klouderone/cornev4promicroedition/Cases/OLED Covers/No Display Cover Right.stp

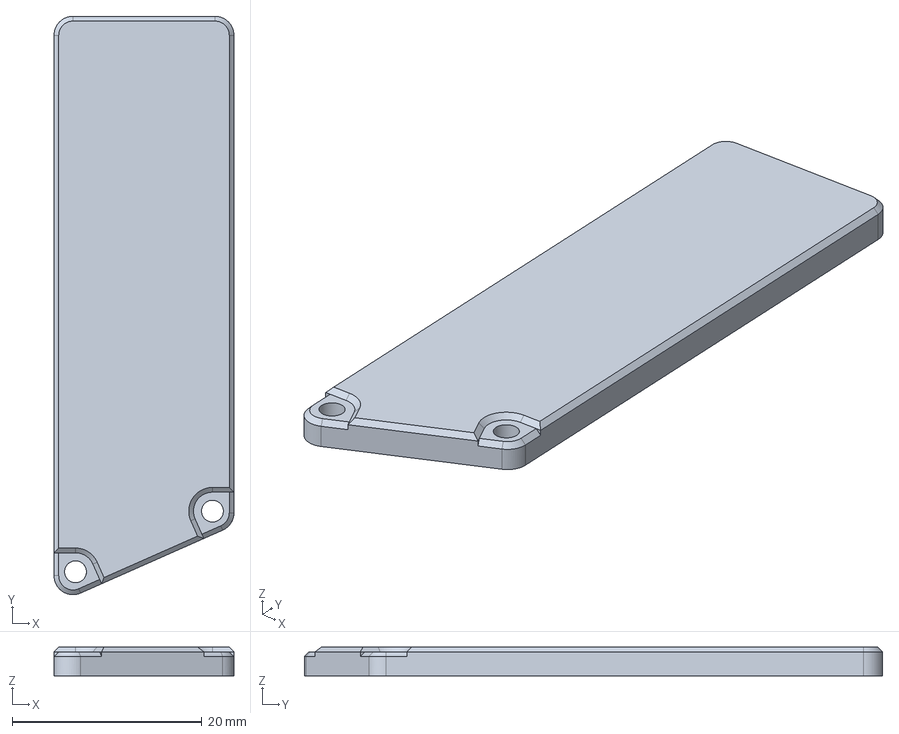
[picture p11: CAD file, 2025-02-16]
Cases/OLED Covers/No Display Cover Right.stp
19.0 x 61.0 x 3.05 mm
