klouderone/cornev4promicroedition/Cases/Switch Plates/Corne V4 PME MX 5 Column Switch Plate Right.stp

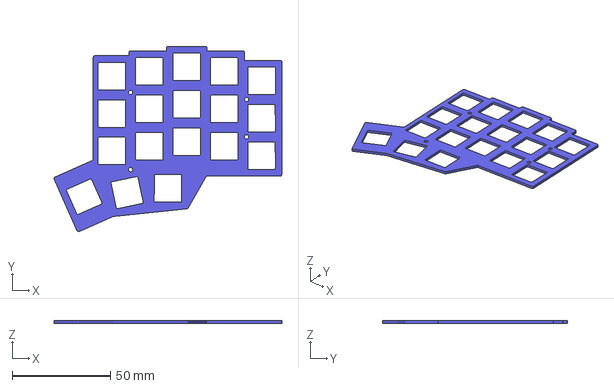
[picture p12: CAD file, 2025-02-16]
Cases/Switch Plates/Corne V4 PME MX 5 Column Switch Plate Right.stp
116.1 x 94.4 x 1.35 mm
