klouderone/cornev4promicroedition/Corne V4 Pro Micro Edition Kicad/left.kicad_sch

## KiCad design Corne V4 Pro Micro Edition Kicad/left.kicad_sch (2025-02-16)

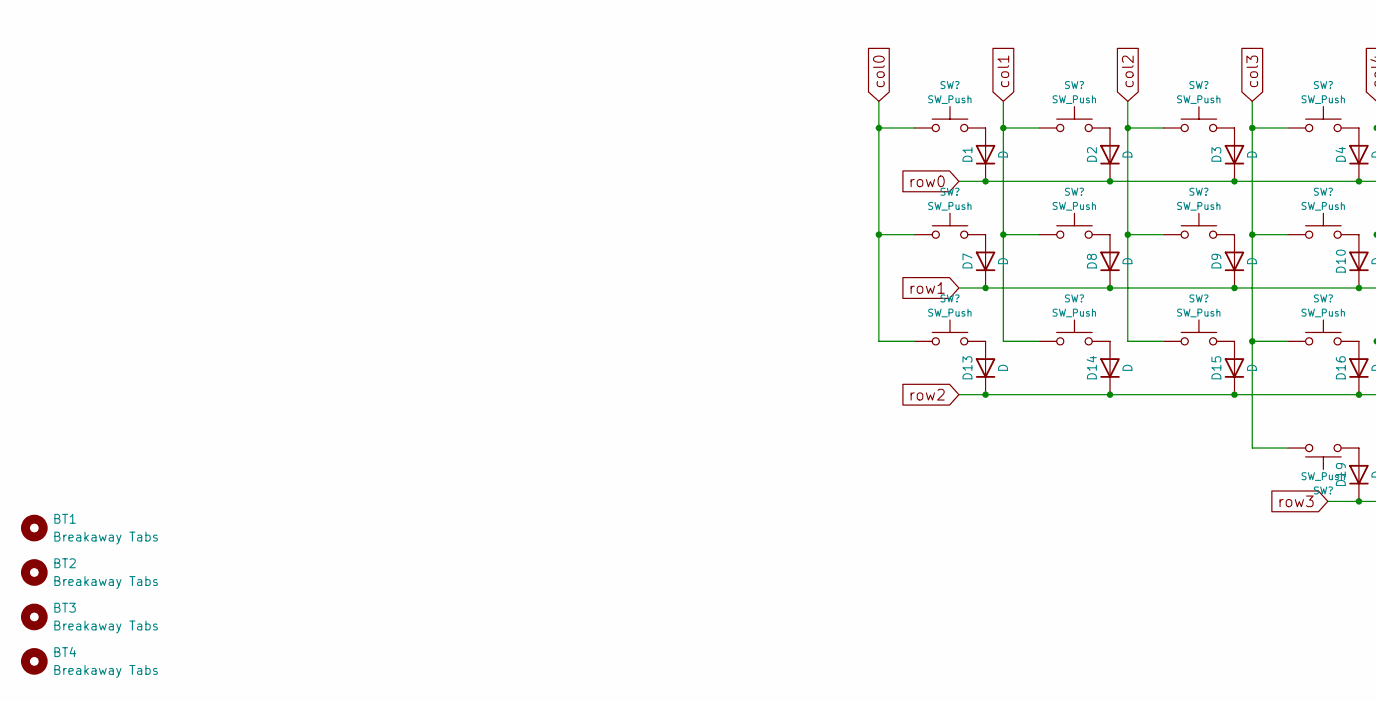
[picture p13: schematic left.kicad_sch, part in row 1, column 1]

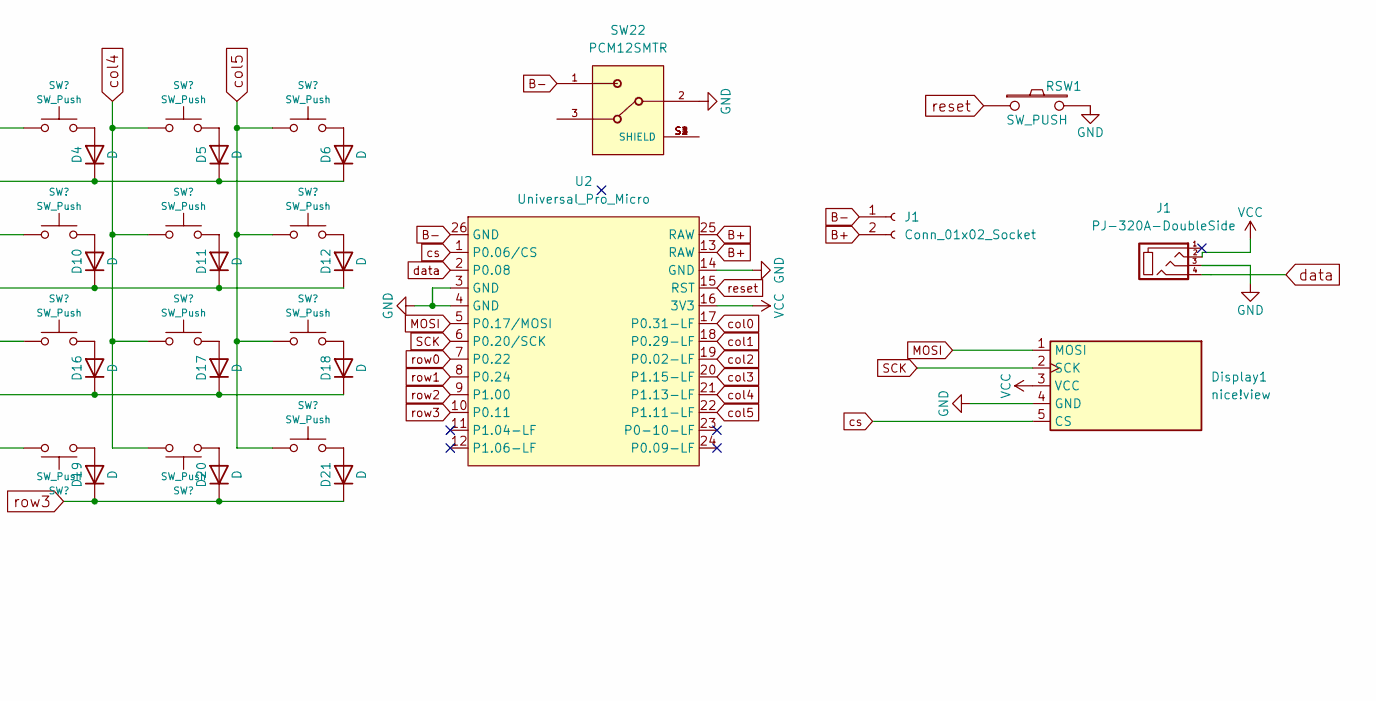
[picture p14: schematic left.kicad_sch, part in row 1, column 2]

Parts:
BT1, BT2, BT3, BT4: Breakaway Tabs; Breakaway_Tabs
D1, D2, D3, D4, D5, D6, D7, D8, D9, D10, D11, D12, D13, D14, D15, D16, D17, D18, D19, D20, D21: D; SMD_SOD123
Display1: nice!view; nice_view
J1: PJ-320A-DoubleSide; TRRS-PJ-320A
RSW1: SW_PUSH; Reset_3x6x4.3
SW1, SW2, SW3, SW4, SW5, SW6, SW7, SW8, SW9, SW10, SW11, SW12, SW13, SW14, SW15, SW16, SW17, SW18, SW19, SW20, SW21: SW_Push; SW_MXchoc_HS_1u
SW22: PCM12SMTR; MSK-12C02 Toggle Switch
U2: Universal_Pro_Micro; Pro_Micro_Footprint_CornePME

Connections:
B+: J1.2, U2.13 (RAW), U2.25 (RAW)
B-: J1.1, SW22.1, U2.26 (GND)
GND: Display1.4 (GND), J1.3, RSW1.2, SW22.2, U2.3 (GND), U2.4 (GND), U2.14 (GND)
MOSI: Display1.1 (MOSI), U2.5 (P0.17/MOSI)
unnamed: D1.2 (A), SW19.2
unnamed: D2.2 (A), SW18.2
unnamed: D3.2 (A), SW13.2
unnamed: D4.2 (A), SW12.2
unnamed: D5.2 (A), SW5.2
unnamed: D6.2 (A), SW4.2
unnamed: D7.2 (A), SW20.2
unnamed: D8.2 (A), SW17.2
unnamed: D9.2 (A), SW14.2
unnamed: D10.2 (A), SW11.2
unnamed: D11.2 (A), SW6.2
unnamed: D12.2 (A), SW3.2
unnamed: D13.2 (A), SW21.2
unnamed: D14.2 (A), SW16.2
unnamed: D15.2 (A), SW15.2
unnamed: D16.2 (A), SW10.2
unnamed: D17.2 (A), SW7.2
unnamed: D18.2 (A), SW2.2
unnamed: D19.2 (A), SW9.1
unnamed: D20.2 (A), SW8.1
unnamed: D21.2 (A), SW1.2
unnamed: SW22.S1 (SHIELD), SW22.S2 (SHIELD), SW22.S3 (SHIELD), SW22.S4 (SHIELD)
SCK: Display1.2 (SCK), U2.6 (P0.20/SCK)
VCC: Display1.3 (VCC), J1.2, U2.16 (3V3)
col0: SW19.1, SW20.1, SW21.1, U2.17 (P0.31-LF)
col1: SW16.1, SW17.1, SW18.1, U2.18 (P0.29-LF)
col2: SW13.1, SW14.1, SW15.1, U2.19 (P0.02-LF)
col3: SW9.2, SW10.1, SW11.1, SW12.1, U2.20 (P1.15-LF)
col4: SW5.1, SW6.1, SW7.1, SW8.2, U2.21 (P1.13-LF)
col5: SW1.1, SW2.1, SW3.1, SW4.1, U2.22 (P1.11-LF)
cs: Display1.5 (CS), U2.1 (P0.06/CS)
data: J1.4, U2.2 (P0.08)
reset: RSW1.1, U2.15 (RST)
row0: D1.1 (K), D2.1 (K), D3.1 (K), D4.1 (K), D5.1 (K), D6.1 (K), U2.7 (P0.22)
row1: D7.1 (K), D8.1 (K), D9.1 (K), D10.1 (K), D11.1 (K), D12.1 (K), U2.8 (P0.24)
row2: D13.1 (K), D14.1 (K), D15.1 (K), D16.1 (K), D17.1 (K), D18.1 (K), U2.9 (P1.00)
row3: D19.1 (K), D20.1 (K), D21.1 (K), U2.10 (P0.11)
