klouderone/cornev4promicroedition/Corne V4 Pro Micro Edition Kicad/right.kicad_sch

## KiCad design Corne V4 Pro Micro Edition Kicad/right.kicad_sch (2025-02-16)

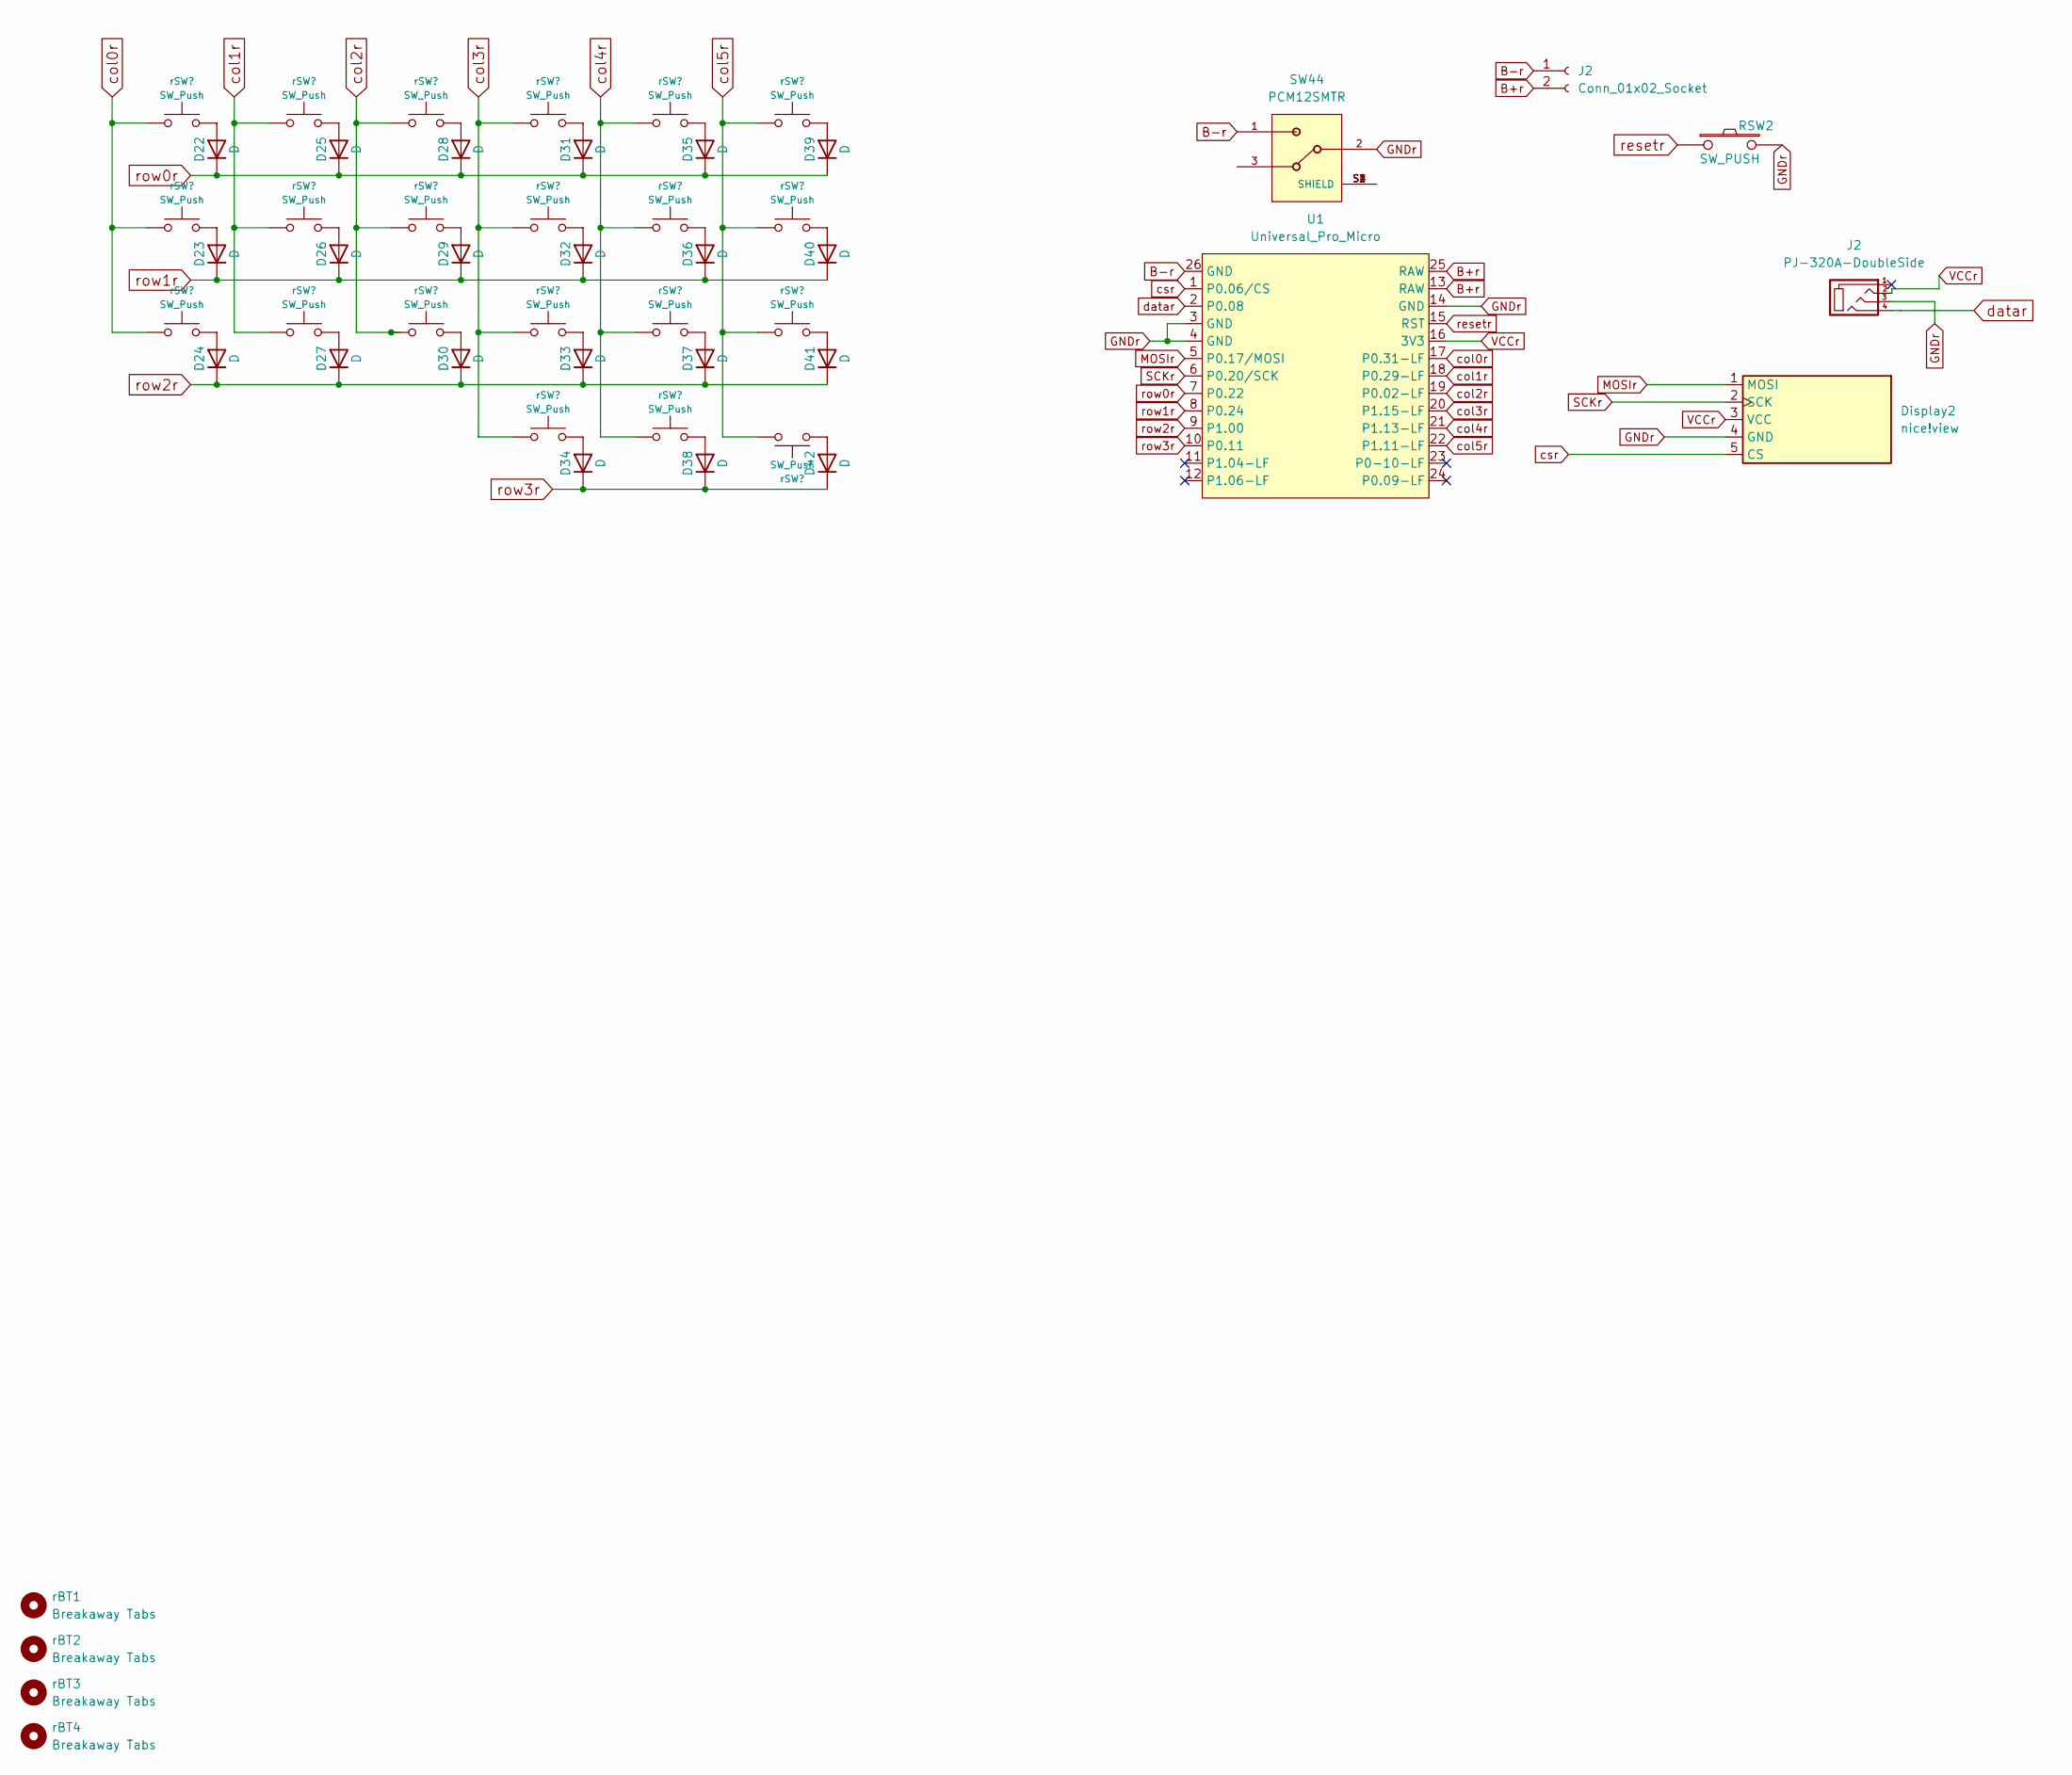
[picture p15: schematic right.kicad_sch]

Parts:
D22, D23, D24, D25, D26, D27, D28, D29, D30, D31, D32, D33, D34, D35, D36, D37, D38, D39, D40, D41, D42: D; SMD_SOD123
Display2: nice!view; nice_view
J2: Conn_01x02_Socket; PH_S2B-PH2-K_1x02_P2.00mm_Horizontal
RSW2: SW_PUSH; Reset_3x6x4.3
SW44: PCM12SMTR; MSK-12C02 Toggle Switch
U1: Universal_Pro_Micro; Pro_Micro_Footprint_CornePME
rBT1, rBT2, rBT3, rBT4: Breakaway Tabs; Breakaway_Tabs
rSW1, rSW2, rSW3, rSW4, rSW5, rSW6, rSW7, rSW8, rSW9, rSW10, rSW11, rSW12, rSW13, rSW14, rSW15, rSW16, rSW17, rSW18, rSW19, rSW20, rSW21: SW_Push; SW_MXchoc_HS_1u

Connections:
B+r: J2.2, U1.13 (RAW), U1.25 (RAW)
B-r: J2.1, SW44.1, U1.26 (GND)
GNDr: Display2.4 (GND), J2.3, RSW2.2, SW44.2, U1.3 (GND), U1.4 (GND), U1.14 (GND)
MOSIr: Display2.1 (MOSI), U1.5 (P0.17/MOSI)
unnamed: D22.2 (A), rSW19.2
unnamed: D23.2 (A), rSW20.2
unnamed: D24.2 (A), rSW21.2
unnamed: D25.2 (A), rSW18.2
unnamed: D26.2 (A), rSW17.2
unnamed: D27.2 (A), rSW16.2
unnamed: D28.2 (A), rSW13.2
unnamed: D29.2 (A), rSW14.2
unnamed: D30.2 (A), rSW15.2
unnamed: D31.2 (A), rSW12.2
unnamed: D32.2 (A), rSW11.2
unnamed: D33.2 (A), rSW10.2
unnamed: D34.2 (A), rSW9.2
unnamed: D35.2 (A), rSW5.2
unnamed: D36.2 (A), rSW6.2
unnamed: D37.2 (A), rSW7.2
unnamed: D38.2 (A), rSW8.2
unnamed: D39.2 (A), rSW4.2
unnamed: D40.2 (A), rSW3.2
unnamed: D41.2 (A), rSW2.2
unnamed: D42.2 (A), rSW1.1
unnamed: SW44.S1 (SHIELD), SW44.S2 (SHIELD), SW44.S3 (SHIELD), SW44.S4 (SHIELD)
SCKr: Display2.2 (SCK), U1.6 (P0.20/SCK)
VCCr: Display2.3 (VCC), J2.2, U1.16 (3V3)
col0r: U1.17 (P0.31-LF), rSW19.1, rSW20.1, rSW21.1
col1r: U1.18 (P0.29-LF), rSW16.1, rSW17.1, rSW18.1
col2r: U1.19 (P0.02-LF), rSW13.1, rSW14.1, rSW15.1
col3r: U1.20 (P1.15-LF), rSW9.1, rSW10.1, rSW11.1, rSW12.1
col4r: U1.21 (P1.13-LF), rSW5.1, rSW6.1, rSW7.1, rSW8.1
col5r: U1.22 (P1.11-LF), rSW1.2, rSW2.1, rSW3.1, rSW4.1
csr: Display2.5 (CS), U1.1 (P0.06/CS)
datar: J2.4, U1.2 (P0.08)
resetr: RSW2.1, U1.15 (RST)
row0r: D22.1 (K), D25.1 (K), D28.1 (K), D31.1 (K), D35.1 (K), D39.1 (K), U1.7 (P0.22)
row1r: D23.1 (K), D26.1 (K), D29.1 (K), D32.1 (K), D36.1 (K), D40.1 (K), U1.8 (P0.24)
row2r: D24.1 (K), D27.1 (K), D30.1 (K), D33.1 (K), D37.1 (K), D41.1 (K), U1.9 (P1.00)
row3r: D34.1 (K), D38.1 (K), D42.1 (K), U1.10 (P0.11)
